ezxzeng/hector36/routed_pcb/mx/images/20260411_213408.jpg

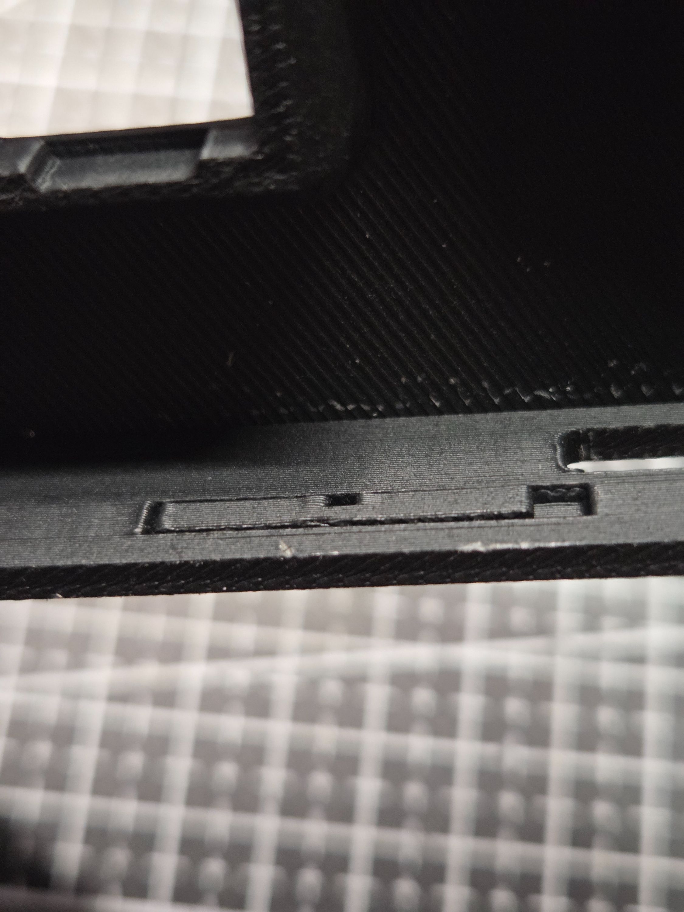
routed_pcb/mx/images/20260411_213408.jpg
